hugomezok/Inversor-SPWM/LTSpice/puenteHconSPWM_IRF.asc

B1: bv; V=if( V(Vtri)> V(Vsin),12,0)
B2: bv; V=if( V(Vtri)> V(Vsin),0,12)
B3: bv; V=if( V(Vtri)> -V(Vsin),12,0)
B4: bv; V=if( V(Vtri)> -V(Vsin),0,12)
B5: bv; V=V(VA)-V(VB)
C1: cap; 2.2µ
D1: diode
D2: diode
D3: diode
D4: diode
L1: ind; {Lfiltro}
M1: nmos; IRF1405
M2: nmos; IRF1405
M3: nmos; IRF1405
M4: nmos; IRF1405
R1: res; 1
R2: res; 4.7
R3: res; 47
R4: res; 4.7
R5: res; 4.7
Rcarga: res; 10K
V1: voltage; SINE(0 12 50)
V2: voltage; PWL REPEAT FOREVER (0 -12 50u 12 100u -12) ENDREPEAT
V3: voltage; 12
Named nets: 0, Vsin, Vtri, AP, AM, BP, BM, VA, VB, Vout
.tran 0 1.1 1 0.01
.step param Lfiltro list 100u 500u 1m
